cubeli27/EpapGadget/Source_Code/Co-op/include/template.h

// private.h template file, rename to private.h and fill in your private data and uncomment lines
#pragma once
#include <cstdint>

// WLAN Zugang hsrw-devices
//const char* WIFI_SSID= "ssid";   
//const char* WIFI_PASSWORD = "password";

//Telegram
//const char* TELEGRAM_BOT_TOKEN = ""; 
//const char* CHAT_ID = ""; 
//const char* USER1_USERNAME = "";
//const char* USER2_USERNAME = "";   
//const char* USER3_USERNAME = "";   

//Displayed strings
//RTC_DATA_ATTR char title[20] = "TITLE";
//RTC_DATA_ATTR char user1[30] = "USER1: ";
//RTC_DATA_ATTR char user2[30] = "USER2: ";
//RTC_DATA_ATTR char user3[30] = "USER3: ";
